Badis007/Rocnikovy_projekt/Fotky/ESP.PNG

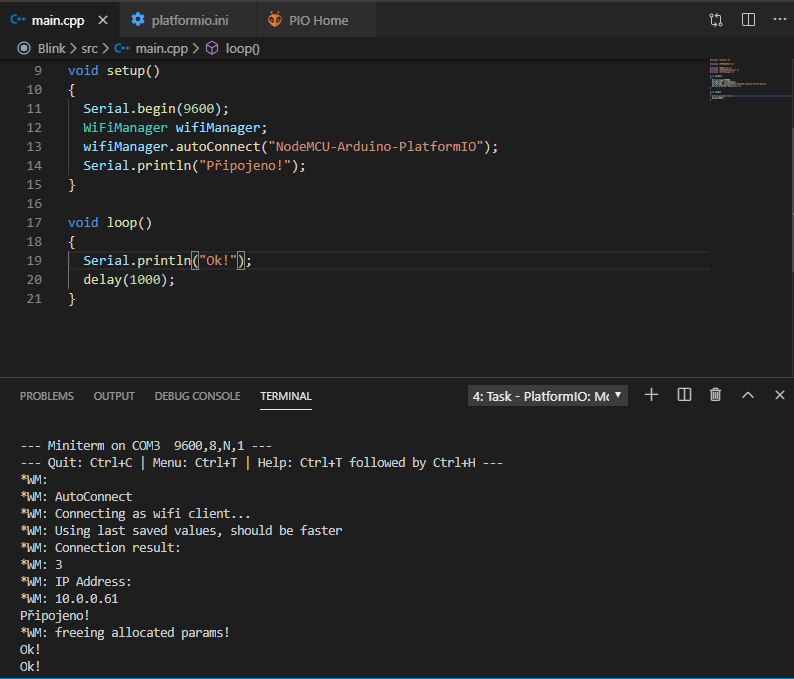
Fotky/ESP.PNG
