Badis007/Rocnikovy_projekt/Fotky/IMG_2076.jpg

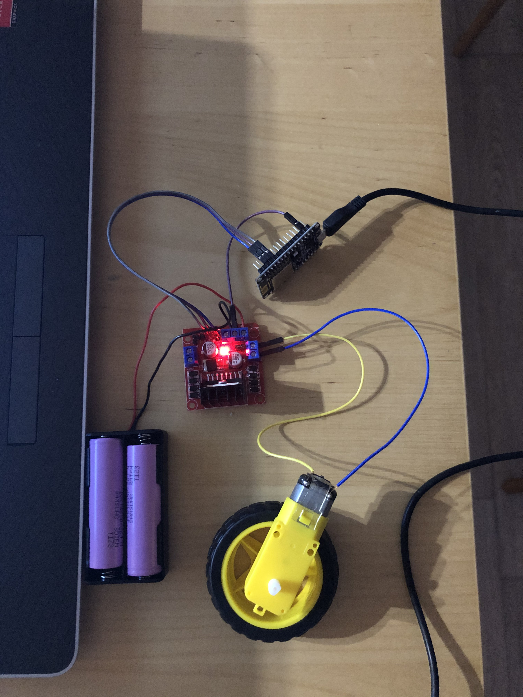
Fotky/IMG_2076.jpg
