Badis007/Rocnikovy_projekt/Fotky/IMG_2077.jpg

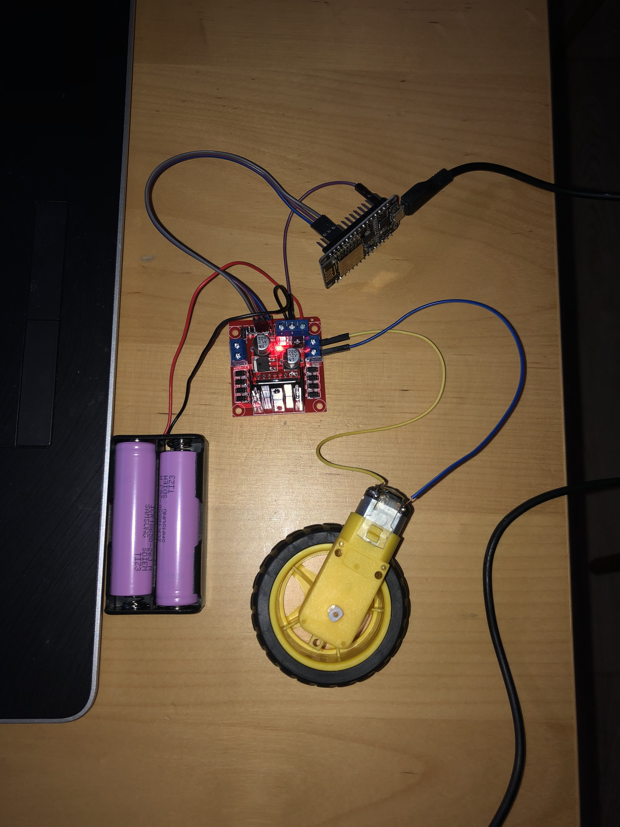
Fotky/IMG_2077.jpg
