Badis007/Rocnikovy_projekt/grafika_aplikace/doprava.png

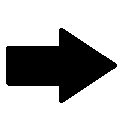
grafika_aplikace/doprava.png
