Badis007/Rocnikovy_projekt/grafika_aplikace/nahoru.png

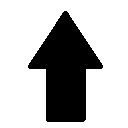
grafika_aplikace/nahoru.png
