Badis007/Rocnikovy_projekt/grafika_aplikace/stop.png

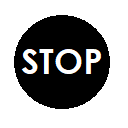
grafika_aplikace/stop.png
