Badis007/Rocnikovy_projekt/Soucastky/3189.jpg

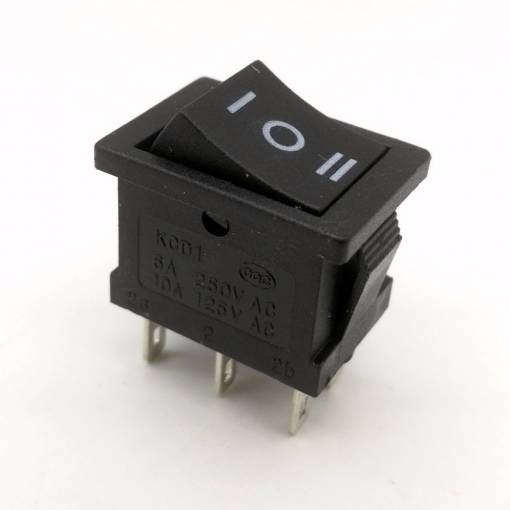
Soucastky/3189.jpg
