Badis007/Rocnikovy_projekt/Soucastky/c27b9a60-d775-4660-9466-9acc67dc5513.jpg

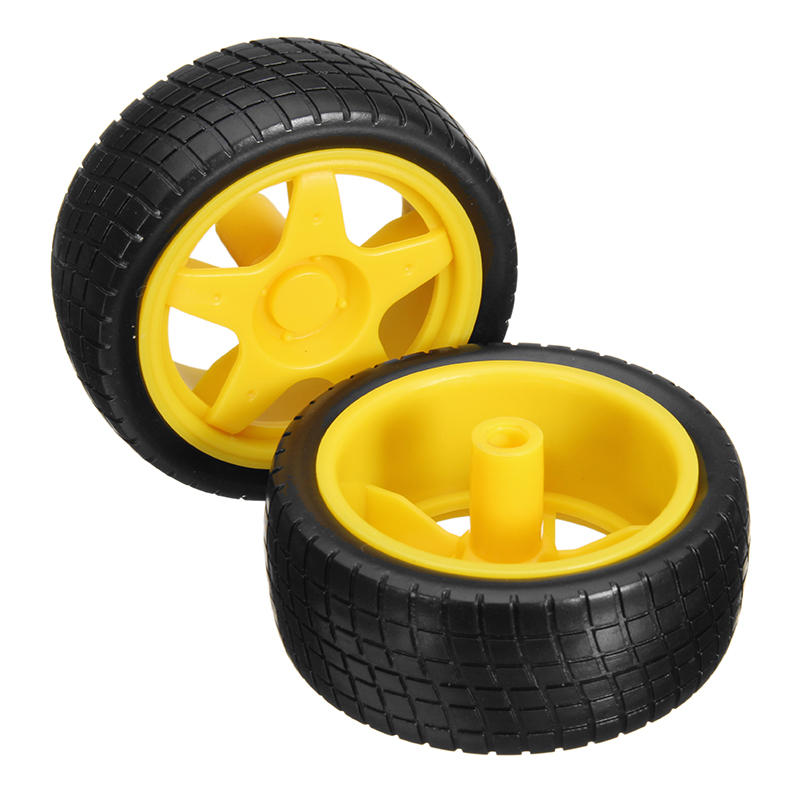
Soucastky/c27b9a60-d775-4660-9466-9acc67dc5513.jpg
