Badis007/Rocnikovy_projekt/Soucastky/PH9226-2-x-aaa-cell-battery-holderImageMain-515.jpg

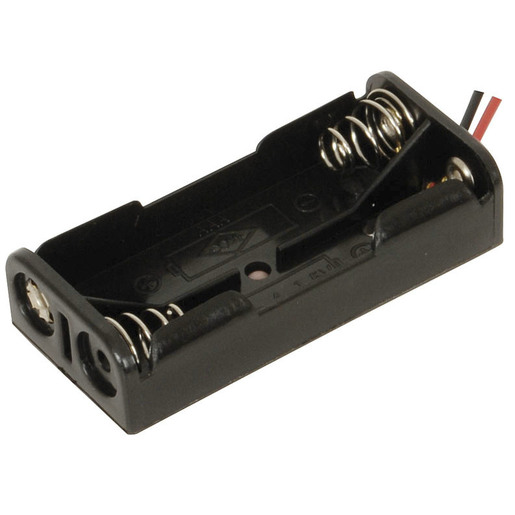
Soucastky/PH9226-2-x-aaa-cell-battery-holderImageMain-515.jpg
