Badis007/Rocnikovy_projekt/Soucastky/quasar-8801-l298n-dc-stepper-motor-driver-controller-board-module-arduino.jpg

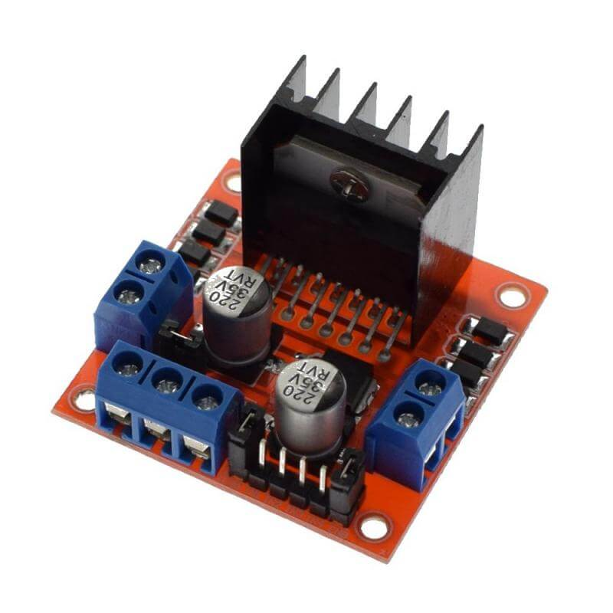
Soucastky/quasar-8801-l298n-dc-stepper-motor-driver-controller-board-module-arduino.jpg
