Badis007/Rocnikovy_projekt/stavba_projektu/79524233_991714277875052_2775989890578382848_n.jpg

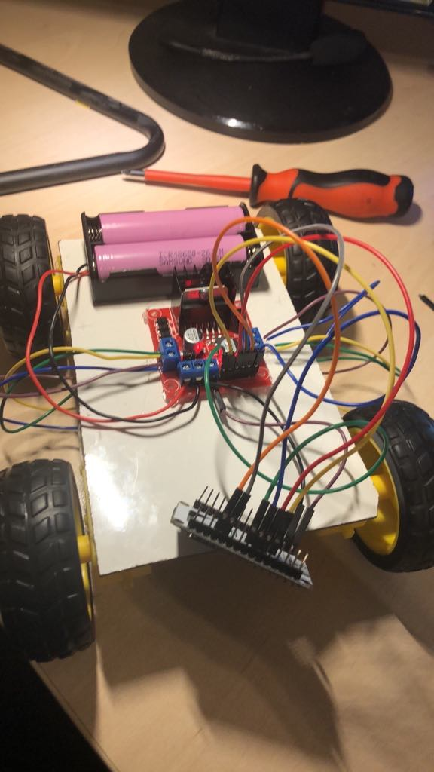
stavba_projektu/79524233_991714277875052_2775989890578382848_n.jpg
