Badis007/Rocnikovy_projekt/stavba_projektu/79601449_435765607299847_2196918395159445504_n.jpg

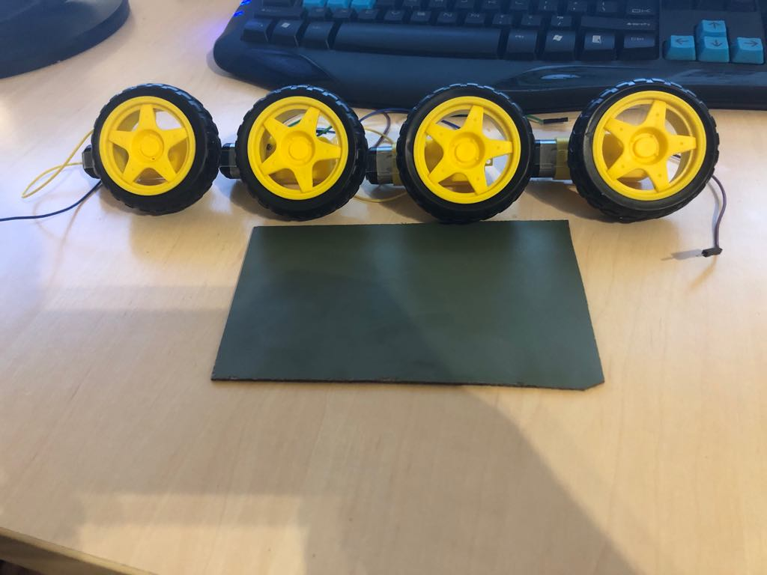
stavba_projektu/79601449_435765607299847_2196918395159445504_n.jpg
