Badis007/Rocnikovy_projekt/stavba_projektu/80448405_1152991858424834_3358993346952429568_n.jpg

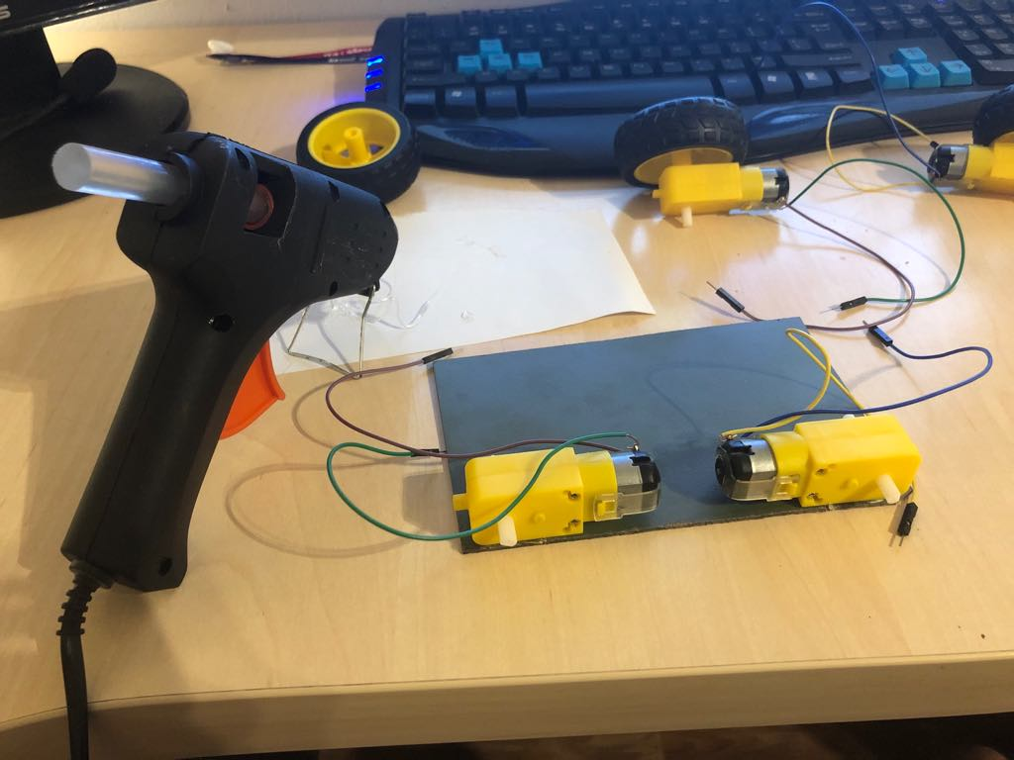
stavba_projektu/80448405_1152991858424834_3358993346952429568_n.jpg
